hznwn/12v-Spa-nningsma-tning-PWM-projekt/Bilder:Video/IMG_0088.JPG

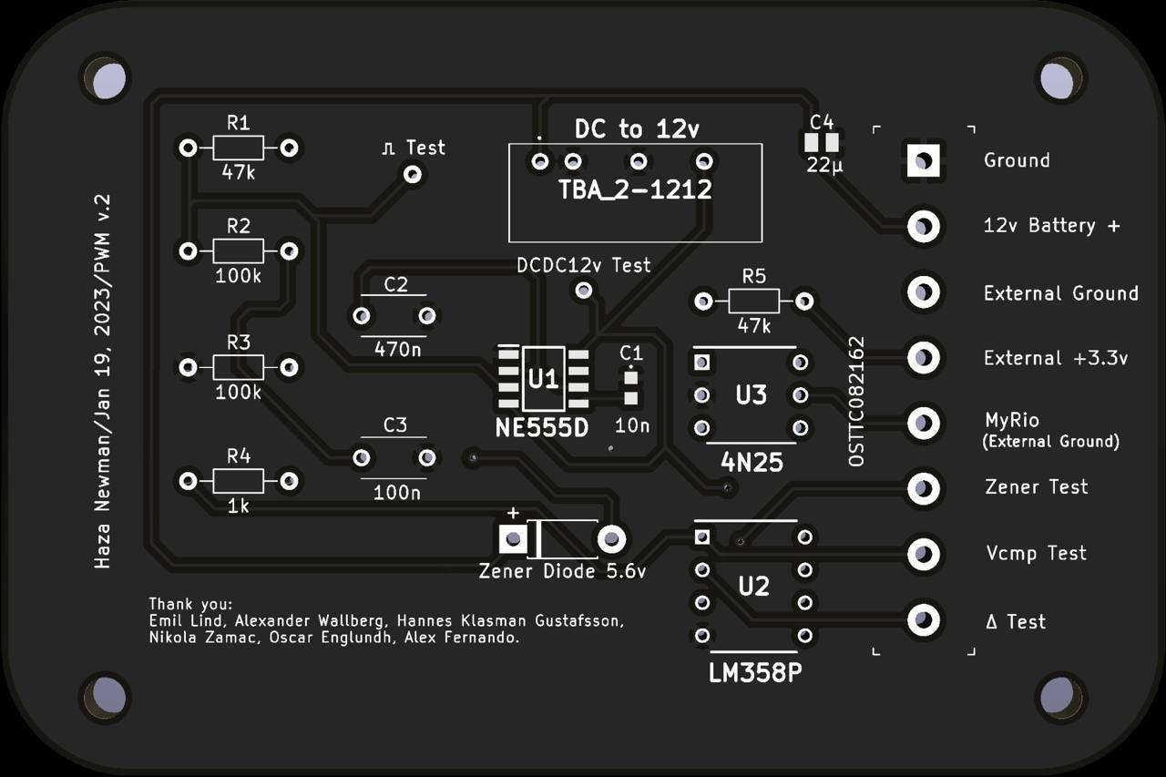
Bilder:Video/IMG_0088.JPG
