hznwn/12v-Spa-nningsma-tning-PWM-projekt/Bilder:Video/IMG_0098.jpeg

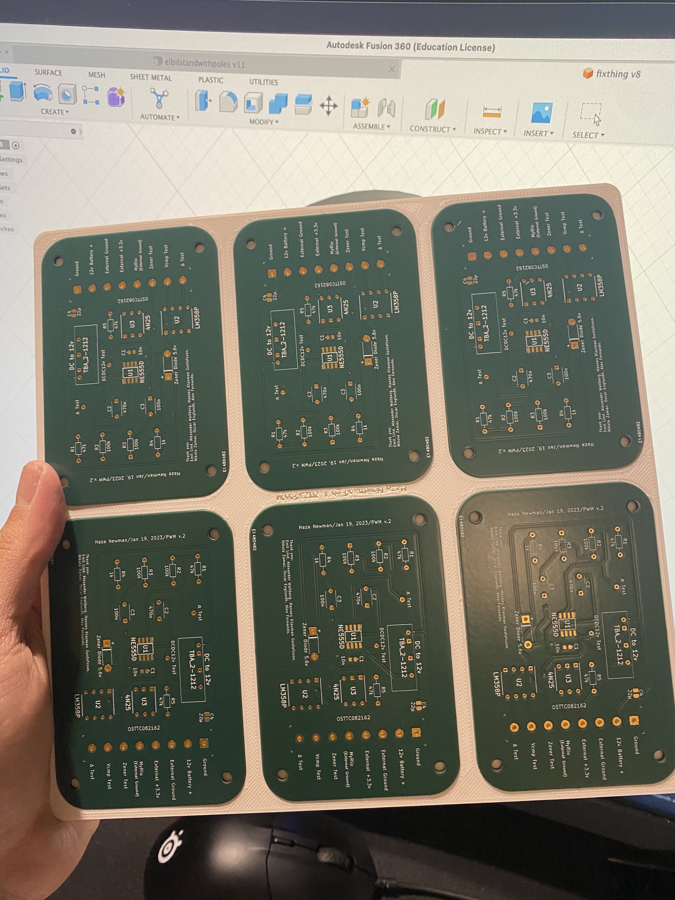
Bilder:Video/IMG_0098.jpeg
