hznwn/12v-Spa-nningsma-tning-PWM-projekt/Bilder:Video/IMG_0205.jpeg

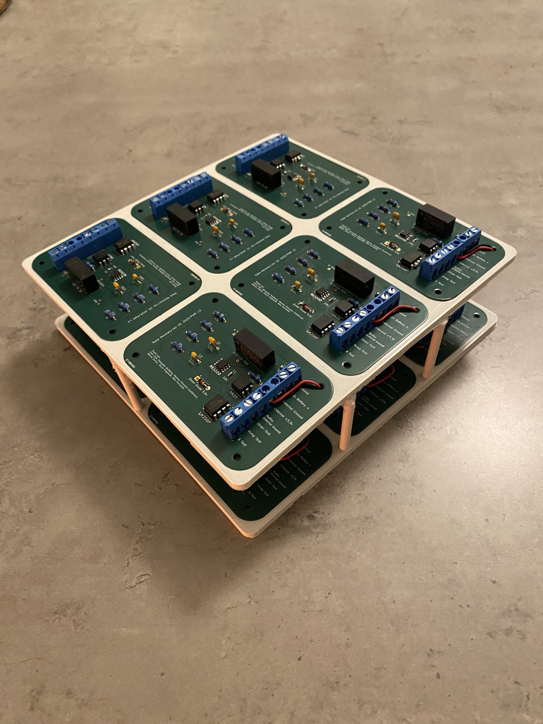
Bilder:Video/IMG_0205.jpeg
