hznwn/12v-Spa-nningsma-tning-PWM-projekt/Bilder:Video/IMG_0206.jpeg

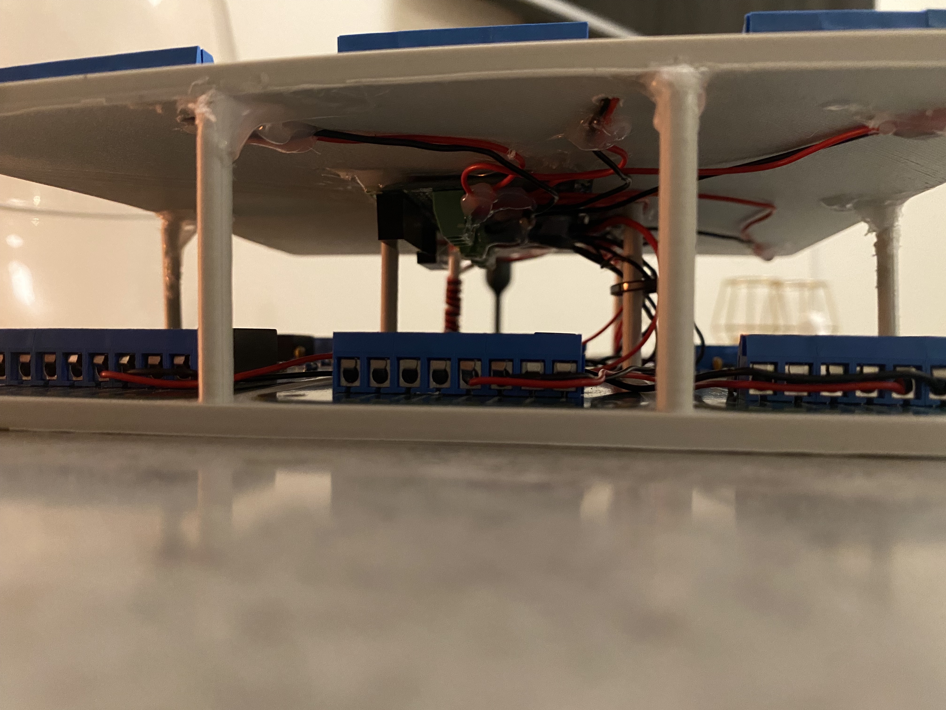
Bilder:Video/IMG_0206.jpeg
